CarVac/vbox/keycap/mx_thumb_right.step

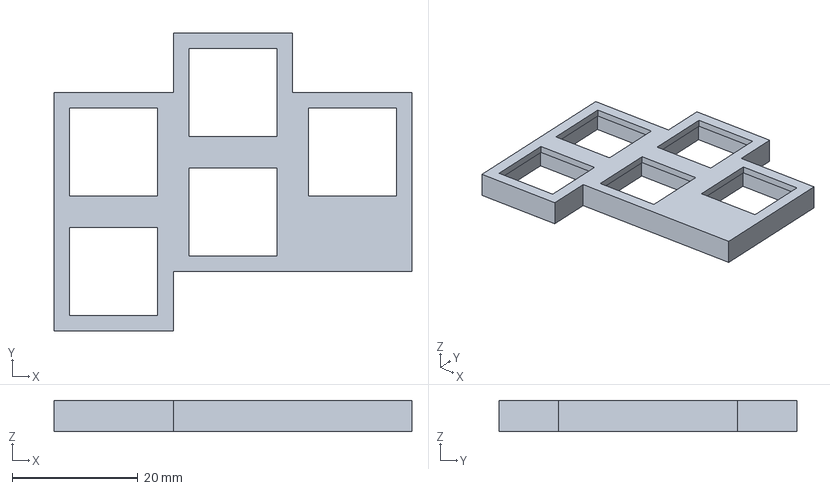
[picture p17: CAD file, 2026-04-28]
keycap/mx_thumb_right.step
57.0 x 47.5 x 5.00 mm
